JanRSmit/HALS-Mechatronics/BASE/Adjust-Level-M8-Screw.png

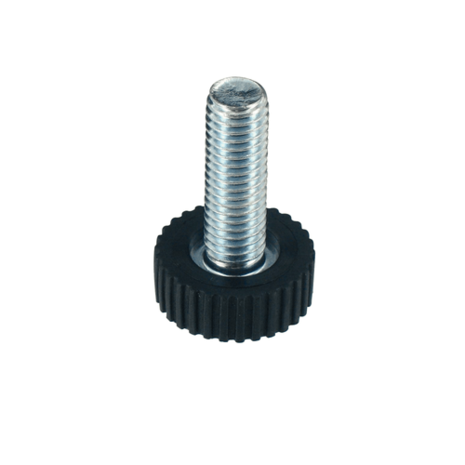
BASE/Adjust-Level-M8-Screw.png
