JanRSmit/HALS-Mechatronics/BASE/Endcap-LevelAdjust-WeightBrackets-02.jpg

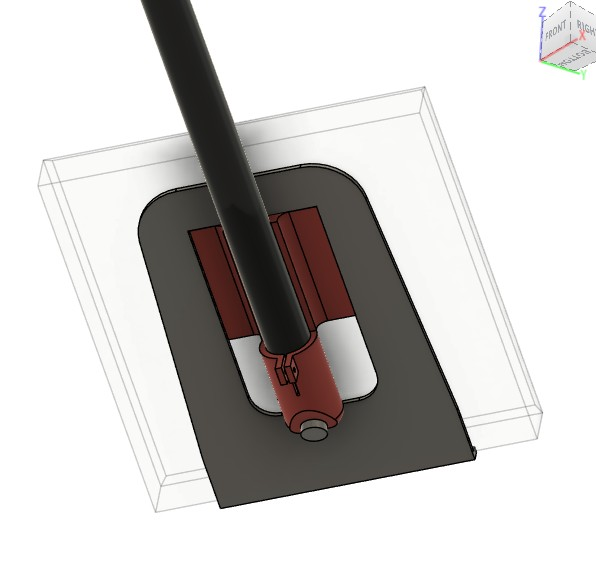
BASE/Endcap-LevelAdjust-WeightBrackets-02.jpg
