JanRSmit/HALS-Mechatronics/BASE/GTSP5212LB_3.jpg

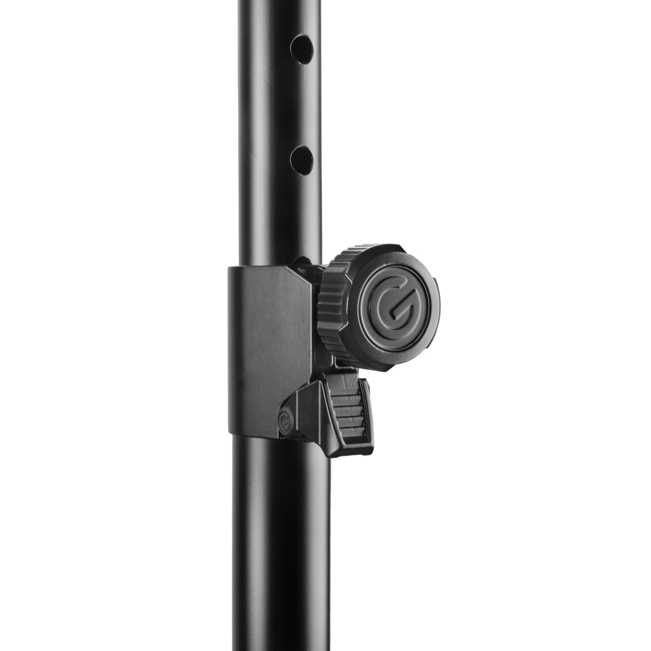
BASE/GTSP5212LB_3.jpg
