JanRSmit/HALS-Mechatronics/Hub-Arm-Assy/Arm-Assy-HUB.png

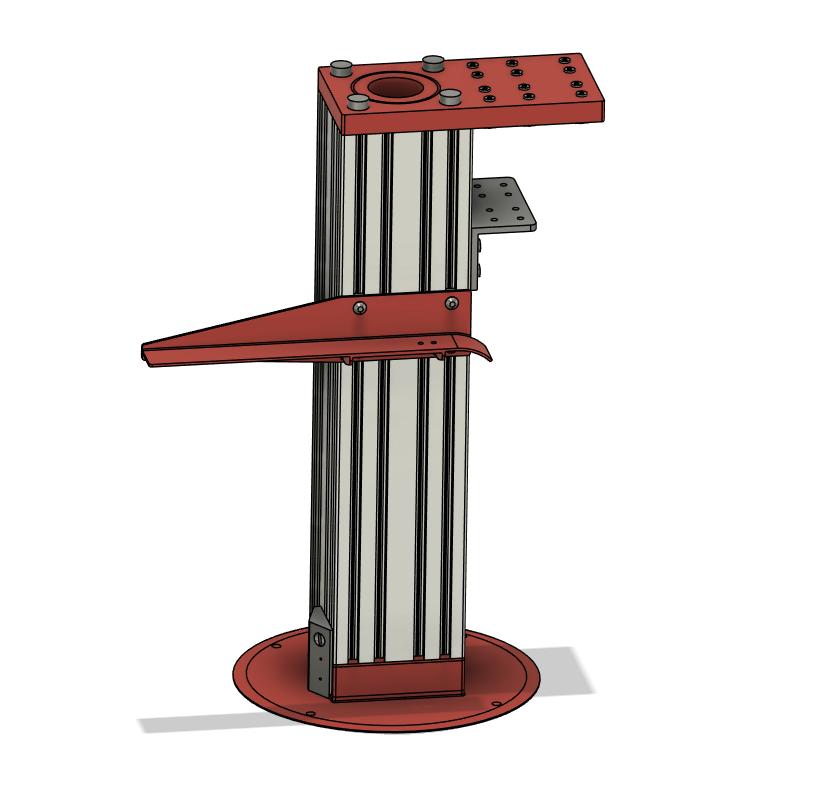
Hub-Arm-Assy/Arm-Assy-HUB.png
