JanRSmit/HALS-Mechatronics/Hub-Arm-Assy/ARM-EIND-SPANBLOK.png

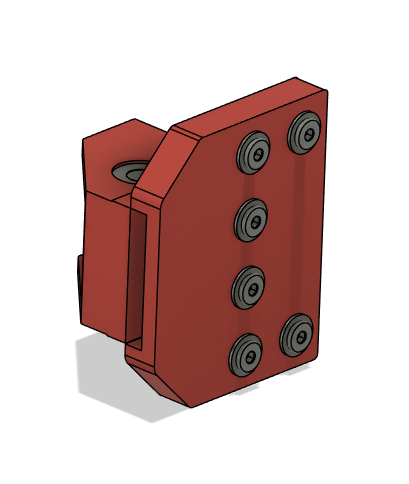
Hub-Arm-Assy/ARM-EIND-SPANBLOK.png
