JanRSmit/HALS-Mechatronics/Hub-Arm-Assy/ARM-MID-Spanblok.png

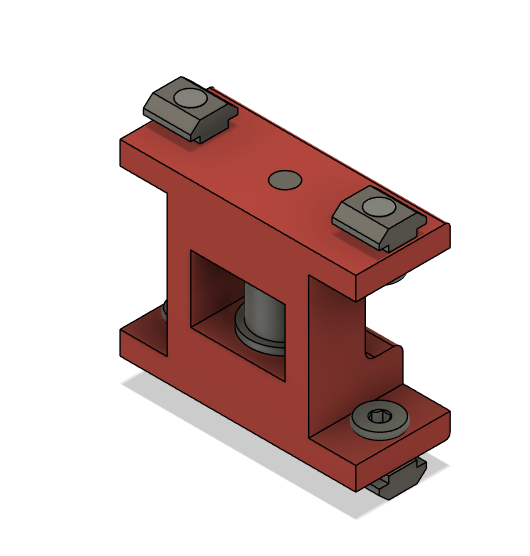
Hub-Arm-Assy/ARM-MID-Spanblok.png
