JanRSmit/HALS-Mechatronics/Hub-Arm-Assy/ARM-MOTOR-MOUNT.png

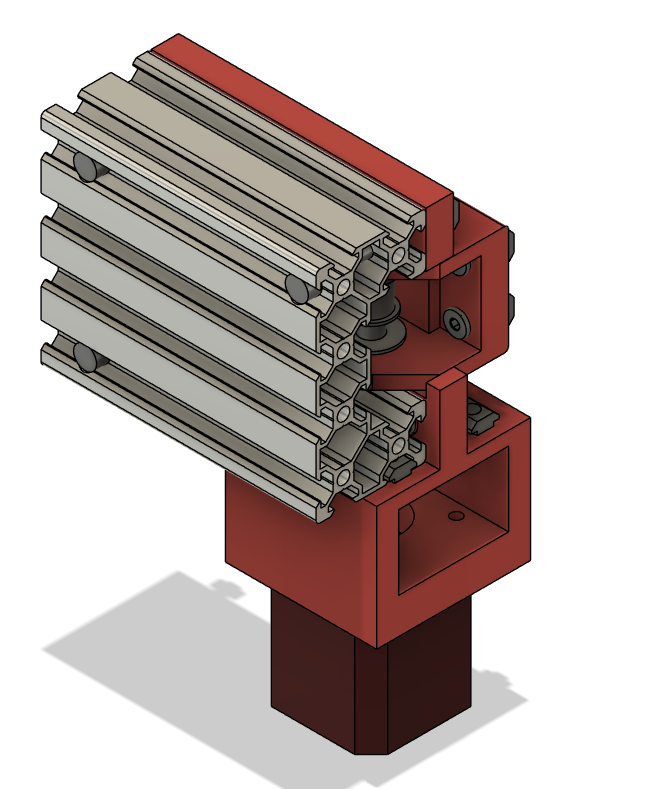
Hub-Arm-Assy/ARM-MOTOR-MOUNT.png
