JanRSmit/HALS-Mechatronics/Hub-Arm-Assy/ECR-P8-6-TPM.jpg

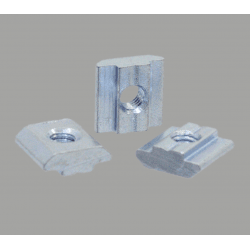
Hub-Arm-Assy/ECR-P8-6-TPM.jpg
