JanRSmit/HALS-Mechatronics/Hub-Arm-Assy/HALS-ROBOT-01.png

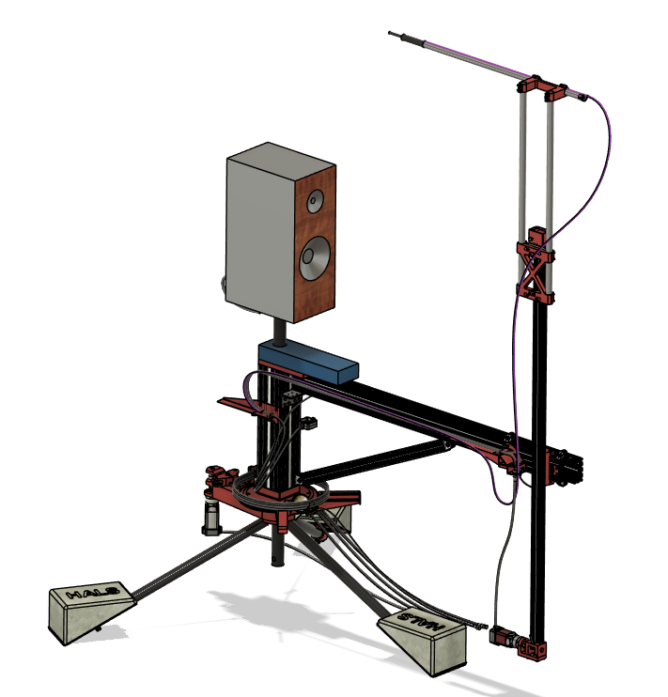
Hub-Arm-Assy/HALS-ROBOT-01.png
