JanRSmit/HALS-Mechatronics/Hub-Arm-Assy/KABEL-HARNAS-Gantry.png

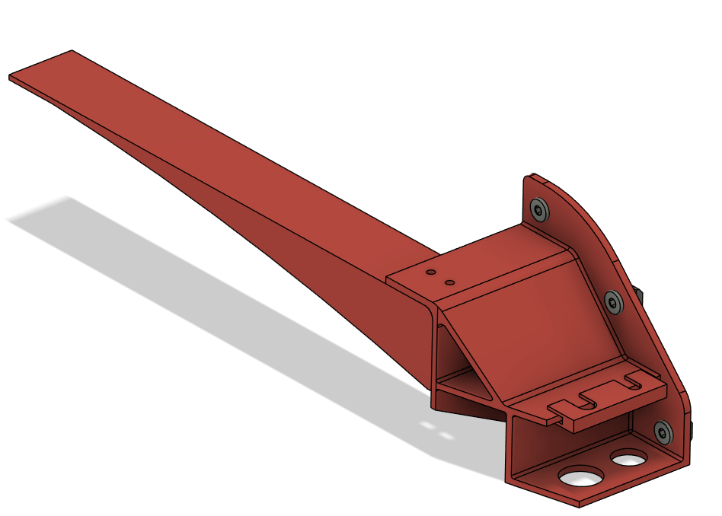
Hub-Arm-Assy/KABEL-HARNAS-Gantry.png
