JanRSmit/HALS-Mechatronics/Hub-Arm-Assy/low-profile-screws-m5x20.jpg

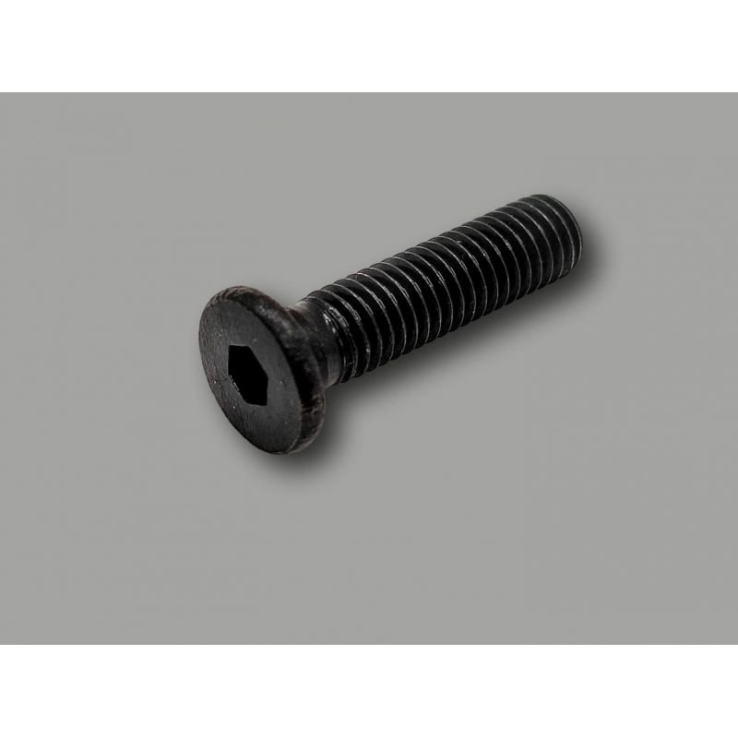
Hub-Arm-Assy/low-profile-screws-m5x20.jpg
