JanRSmit/HALS-Mechatronics/Hub-Arm-Assy/Pivot-joint-for-20x40-profile.jpg

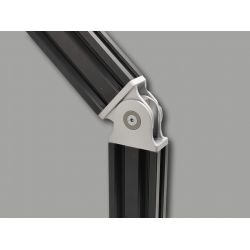
Hub-Arm-Assy/Pivot-joint-for-20x40-profile.jpg
