JanRSmit/HALS-Mechatronics/Hub-Arm-Assy/Top-support-of-Hub-Arm-Assy-vertical-crossection.jpg

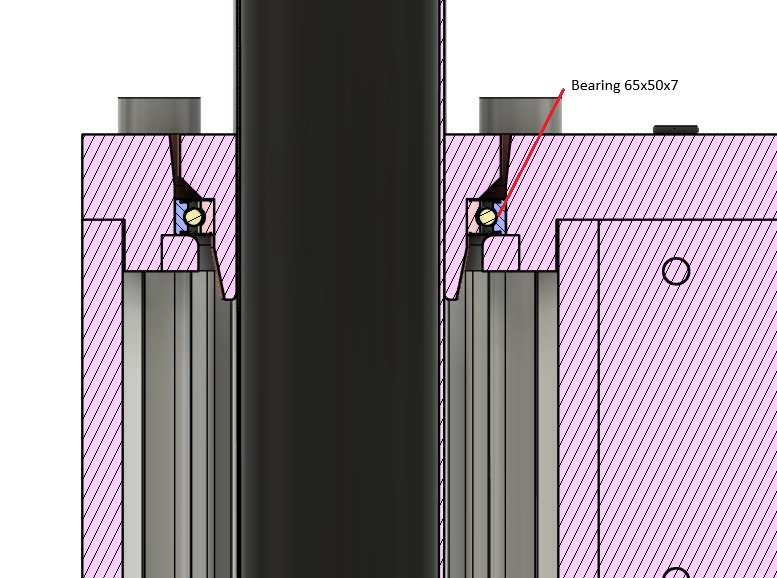
Hub-Arm-Assy/Top-support-of-Hub-Arm-Assy-vertical-crossection.jpg
