JanRSmit/HALS-Mechatronics/MOTION&CABLING/3D-Model-CABLING.jpg

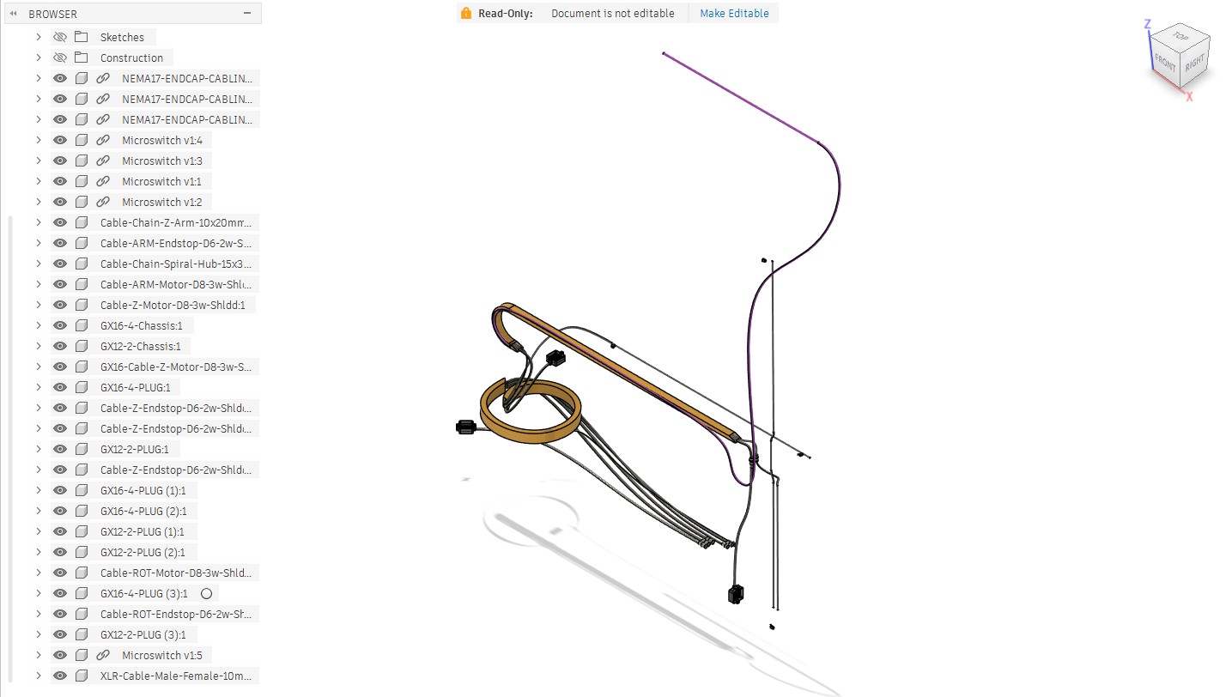
MOTION&CABLING/3D-Model-CABLING.jpg
