JanRSmit/HALS-Mechatronics/MOTION&CABLING/GitHub-MOTION (Electronics-Motors)/BTT-Stuff/GRBLHAL-BTTSKR3EZ-Firmware-01/02-Screenshot 2026-01-21.png

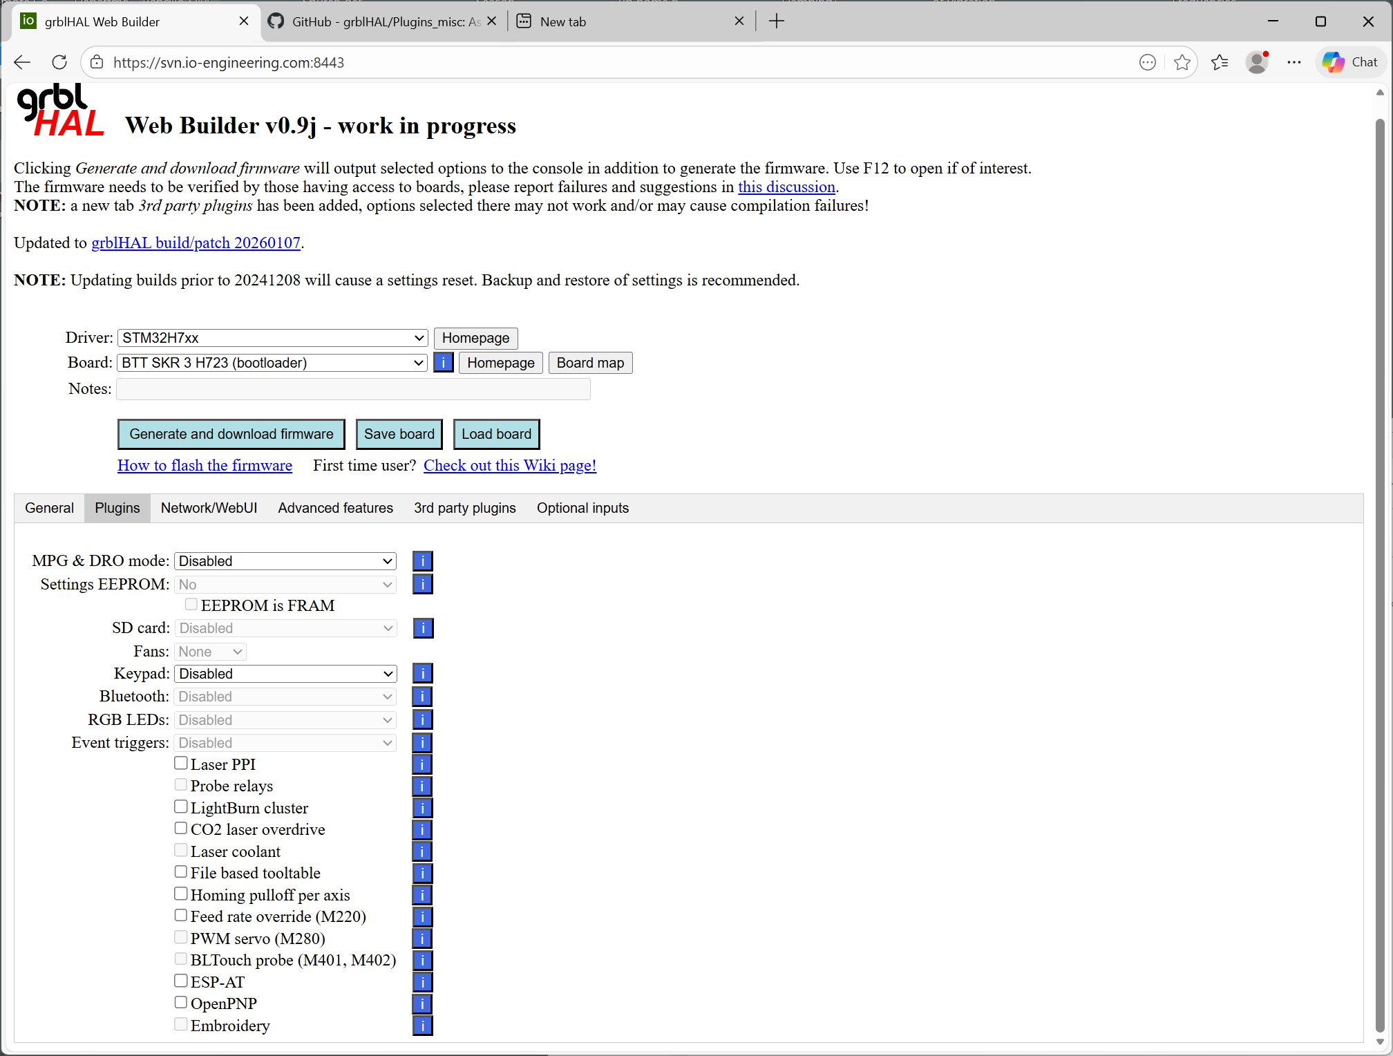
MOTION&CABLING/GitHub-MOTION (Electronics-Motors)/BTT-Stuff/GRBLHAL-BTTSKR3EZ-Firmware-01/02-Screenshot 2026-01-21.png
