JanRSmit/HALS-Mechatronics/MOTION&CABLING/GitHub-MOTION (Electronics-Motors)/BTT-Stuff/Hardware (SKR 3 EZ)/EXT2-Connections-needed.png

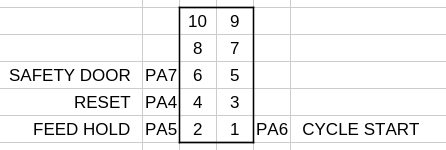
MOTION&CABLING/GitHub-MOTION (Electronics-Motors)/BTT-Stuff/Hardware (SKR 3 EZ)/EXT2-Connections-needed.png
