JanRSmit/HALS-Mechatronics/MOTION&CABLING/Motion-Controller-Schema.jpg

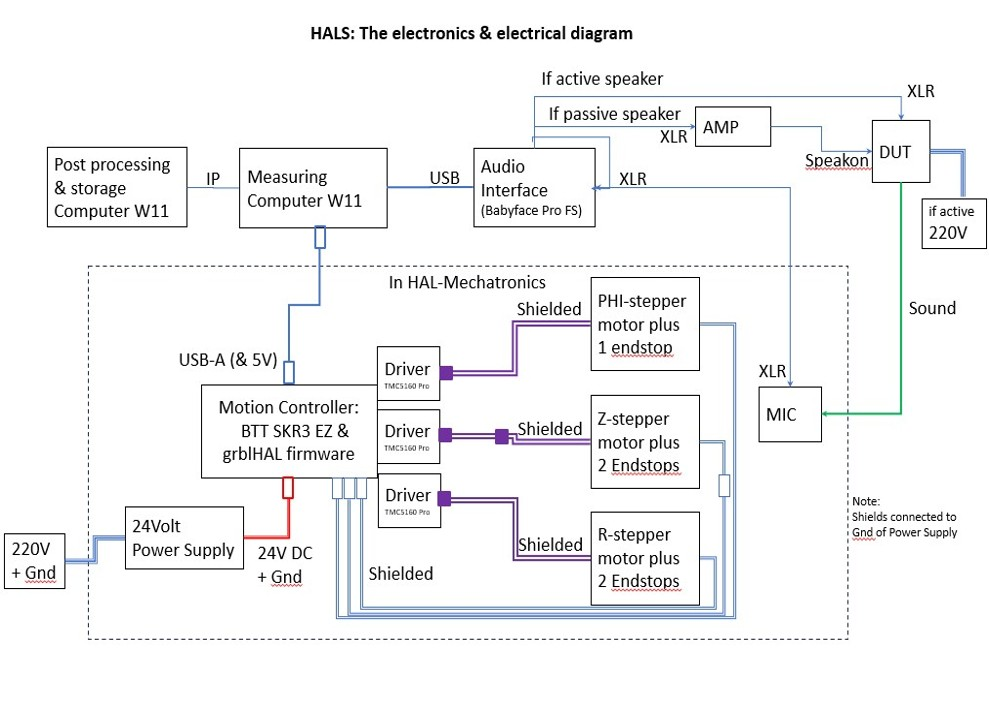
MOTION&CABLING/Motion-Controller-Schema.jpg
