JanRSmit/HALS-Mechatronics/RotatingDrive/Motor-Pulley-Assy-complete.jpg

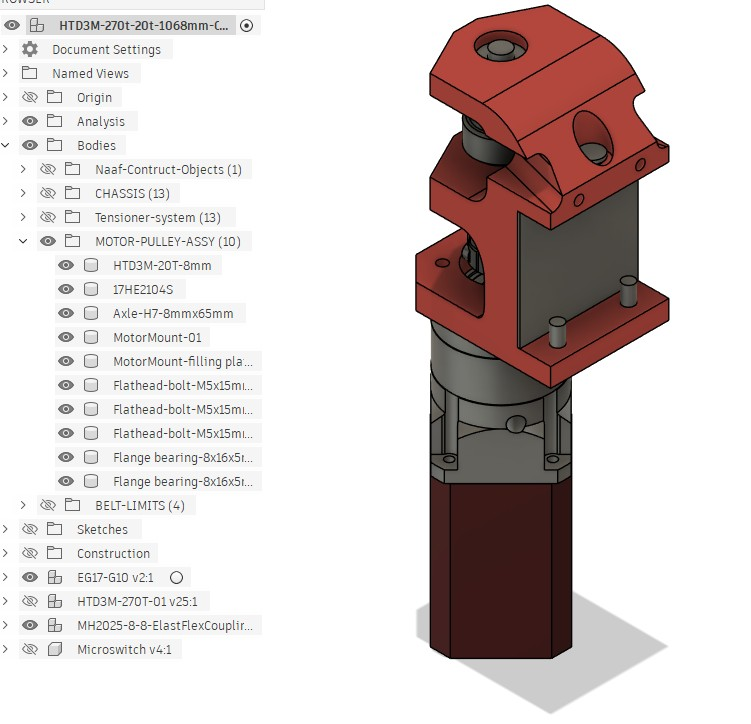
RotatingDrive/Motor-Pulley-Assy-complete.jpg
