JanRSmit/HALS-Mechatronics/RotatingDrive/Nema17-Endcap-Cabling.jpg

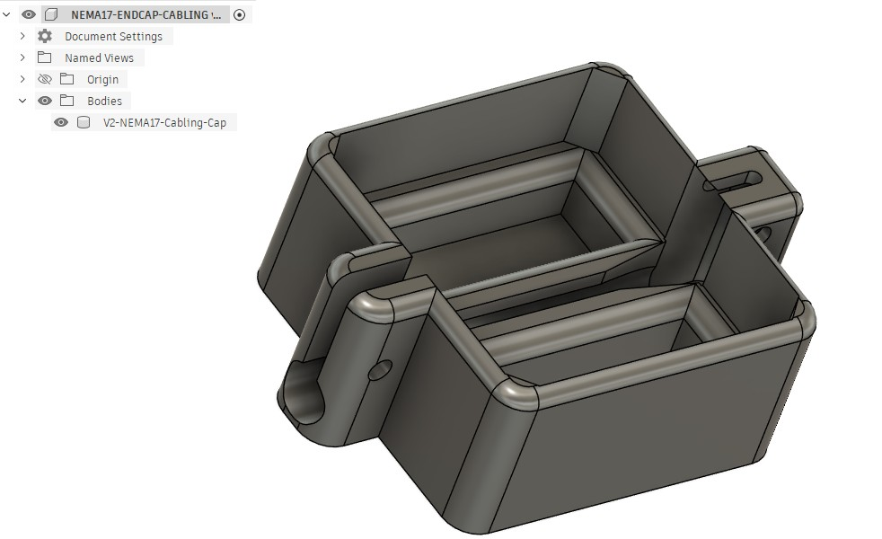
RotatingDrive/Nema17-Endcap-Cabling.jpg
