JanRSmit/HALS-Mechatronics/RotatingDrive/Screenshot 2026-04-07 114829.jpg

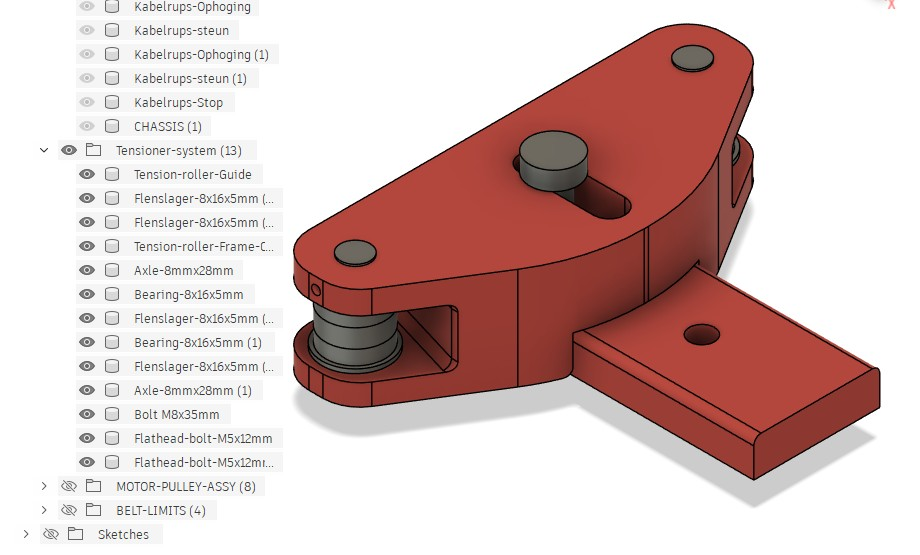
RotatingDrive/Screenshot 2026-04-07 114829.jpg
