JanRSmit/HALS-Mechatronics/RotatingDrive/Tensioner-system-Assy.jpg

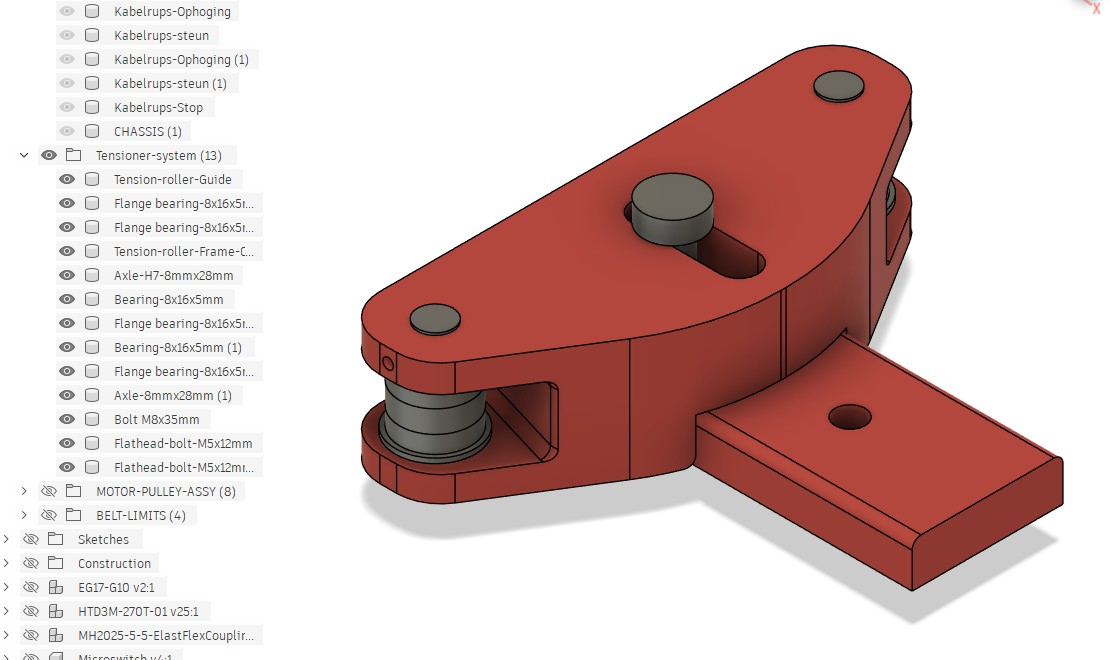
RotatingDrive/Tensioner-system-Assy.jpg
