JanRSmit/HALS-Mechatronics/STOOL/20260924_093839.jpg

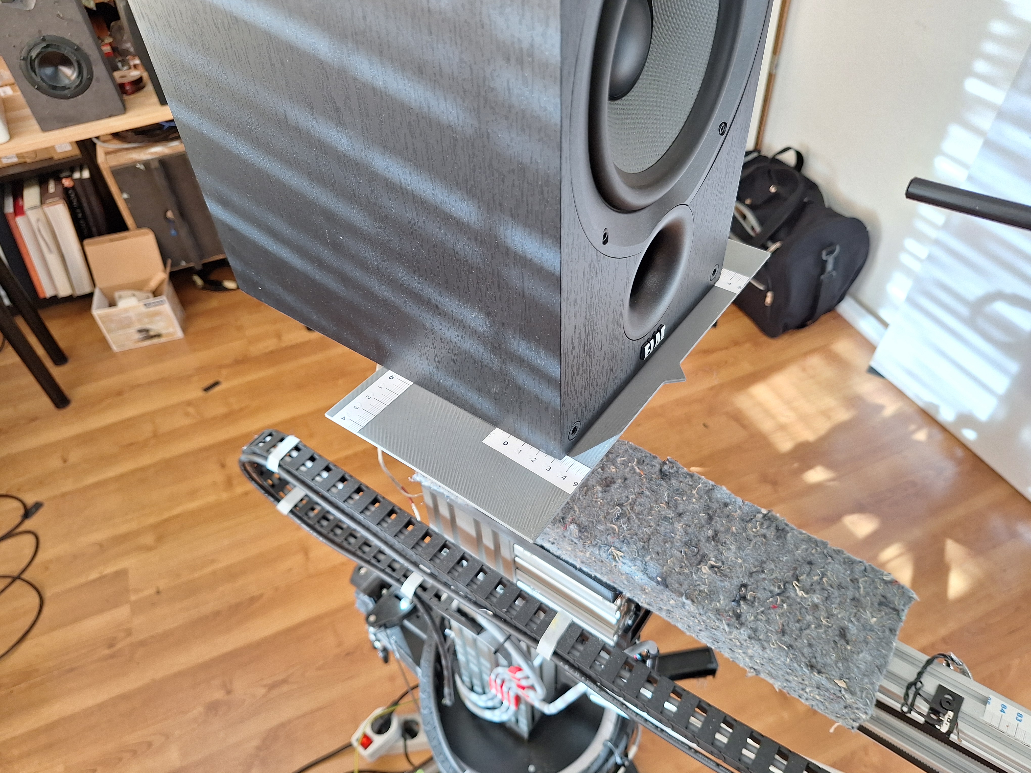
STOOL/20260924_093839.jpg
