JanRSmit/HALS-Mechatronics/STOOL/Stool-9x90mm-incl-CalibTriangle.jpg

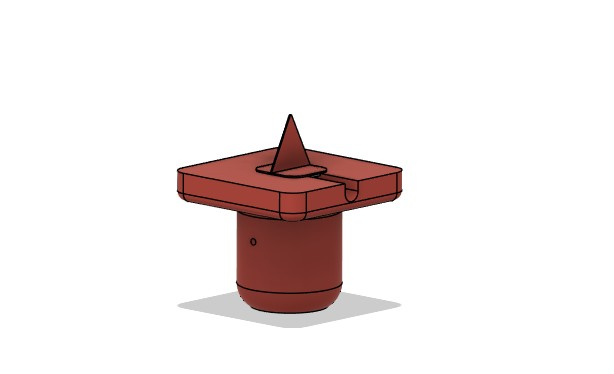
STOOL/Stool-9x90mm-incl-CalibTriangle.jpg
