JanRSmit/HALS-Mechatronics/STOOL/Stool-200x200m-incl-CalibTriangle.jpg

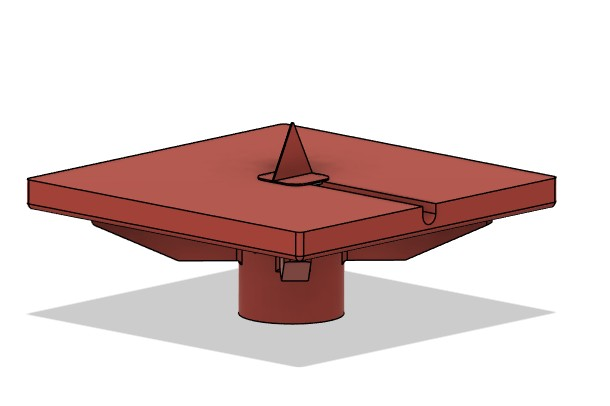
STOOL/Stool-200x200m-incl-CalibTriangle.jpg
