JanRSmit/HALS-Mechatronics/BASE/TripodLeg-Mass-Plateau.step

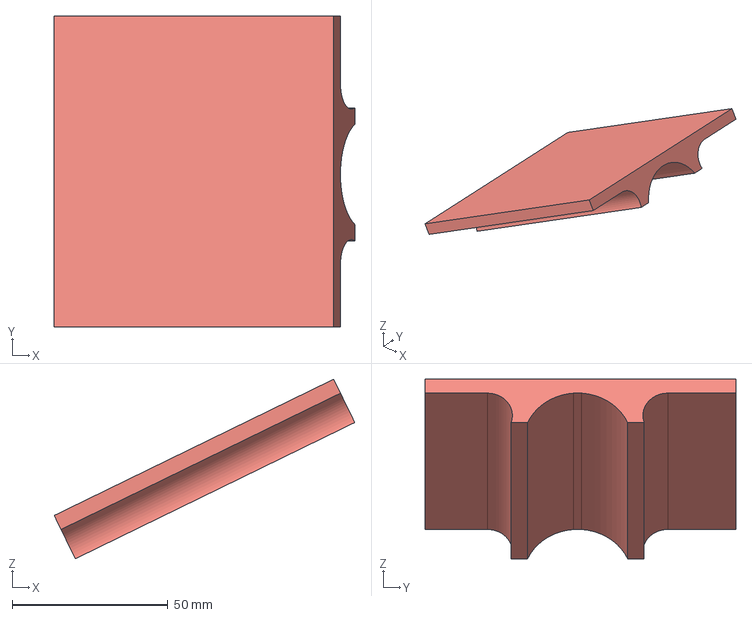
[picture p81: CAD file, 2026-04-06]
BASE/TripodLeg-Mass-Plateau.step
96.7 x 100.0 x 57.8 mm
