JanRSmit/HALS-Mechatronics/RotatingDrive/Tension-Roller-Frame.step

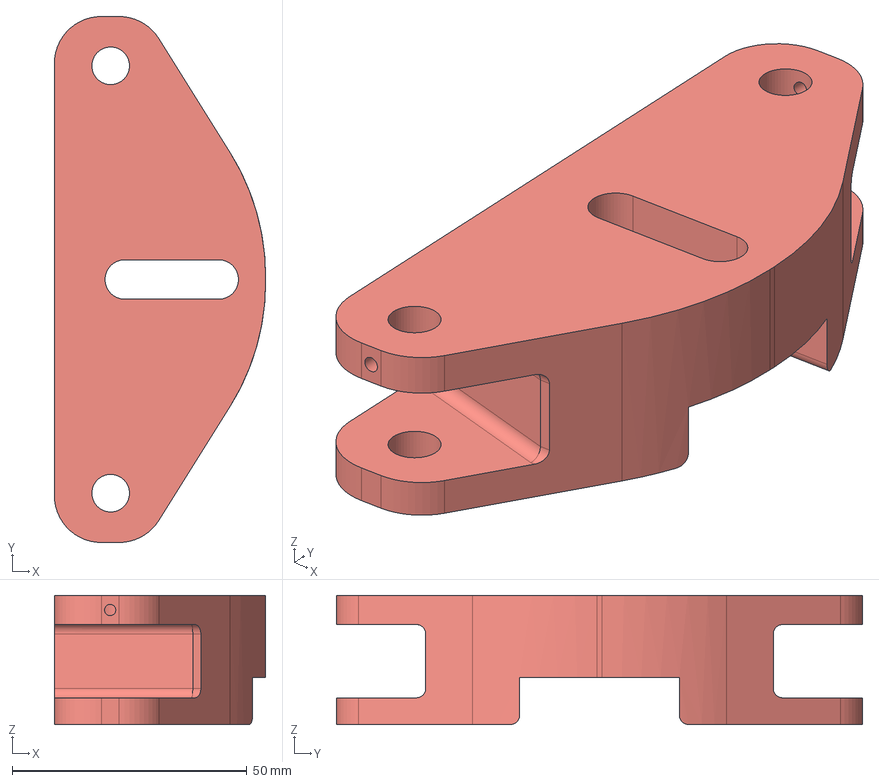
[picture p82: CAD file, 2026-04-07]
RotatingDrive/Tension-Roller-Frame.step
45.0 x 112.0 x 27.5 mm
