JanRSmit/HALS-Mechatronics/BASE/TripodLeg-Endcaps.step

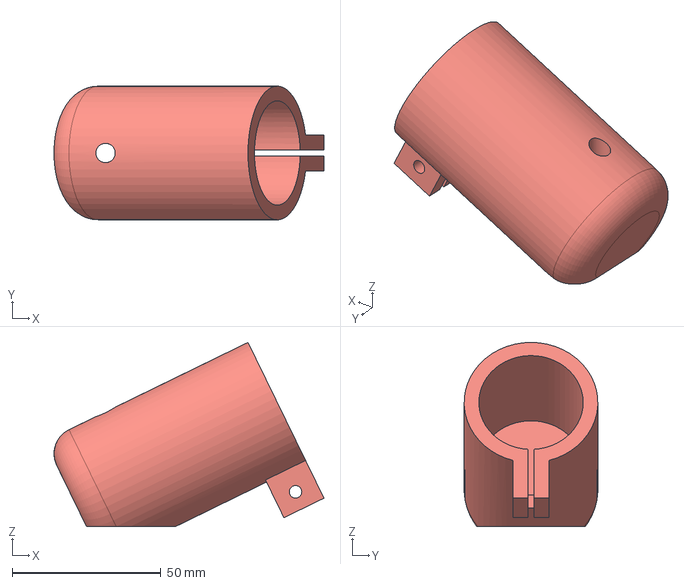
[picture p83: CAD file, 2026-04-06]
BASE/TripodLeg-Endcaps.step
90.8 x 45.0 x 62.0 mm
