JanRSmit/HALS-Mechatronics/RotatingDrive/CableChain-Mount-Chassis-Side.step

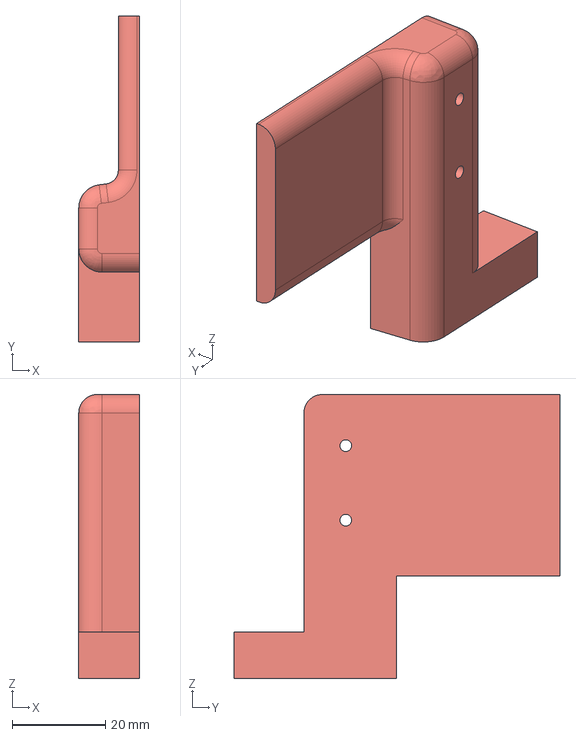
[picture p84: CAD file, 2026-04-07]
RotatingDrive/CableChain-Mount-Chassis-Side.step
13.0 x 70.0 x 61.0 mm
