JanRSmit/HALS-Mechatronics/BASE/TripodLeg-Endcap-WeightBrackes-adjust-foot.step

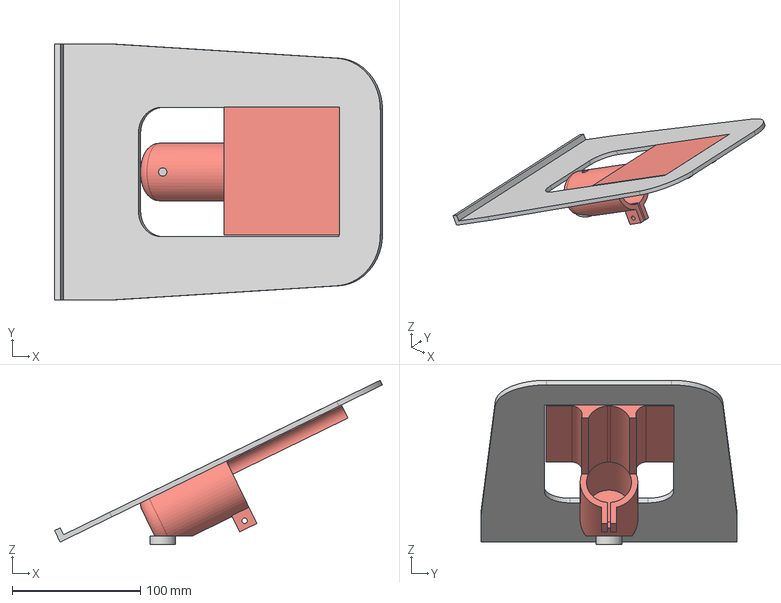
[picture p85: CAD file, 2026-03-27]
BASE/TripodLeg-Endcap-WeightBrackes-adjust-foot.step
256.0 x 200.0 x 128.4 mm
