JanRSmit/HALS-Mechatronics/RotatingDrive/Cablechain-Support-Part-2.step

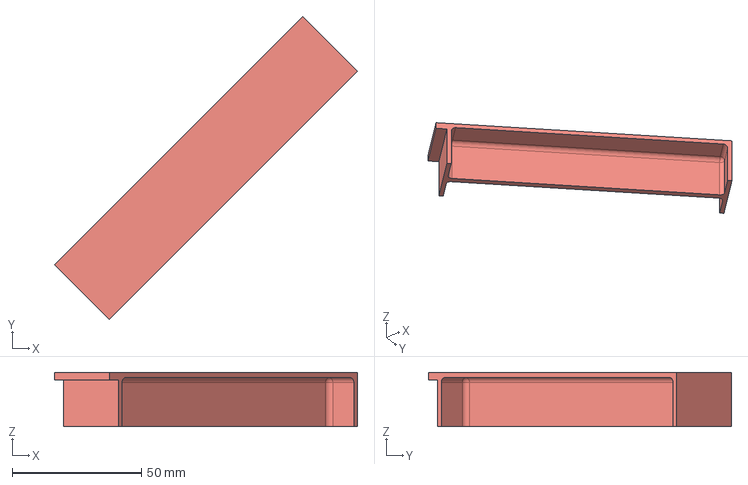
[picture p86: CAD file, 2026-04-07]
RotatingDrive/Cablechain-Support-Part-2.step
117.4 x 117.4 x 21.0 mm
