JanRSmit/HALS-Mechatronics/RotatingDrive/NEMA17-ENDCAP-CABLING.step

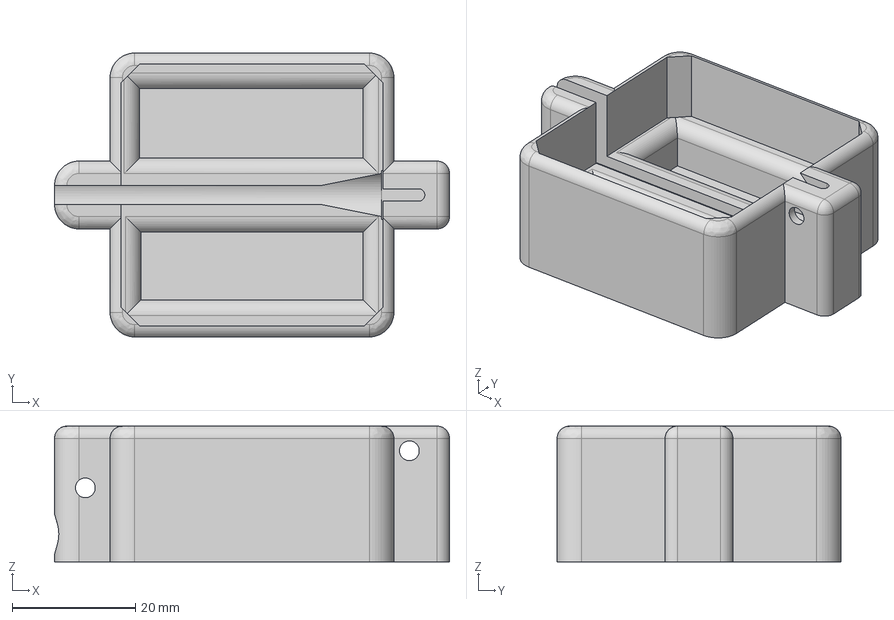
[picture p87: CAD file, 2026-04-07]
RotatingDrive/NEMA17-ENDCAP-CABLING.step
64.0 x 46.0 x 22.0 mm
