JanRSmit/HALS-Mechatronics/RotatingDrive/MSwitch-Bracket-Clamp.step

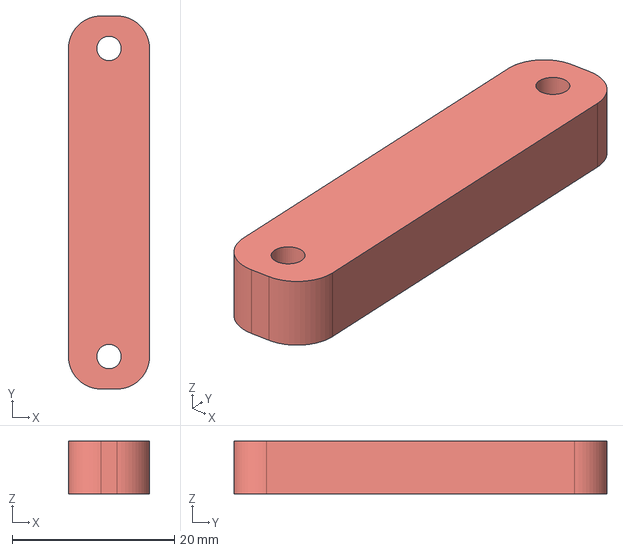
[picture p88: CAD file, 2026-04-07]
RotatingDrive/MSwitch-Bracket-Clamp.step
10.0 x 46.0 x 6.50 mm
