JanRSmit/HALS-Mechatronics/RotatingDrive/Tension-Roller-Guide.step

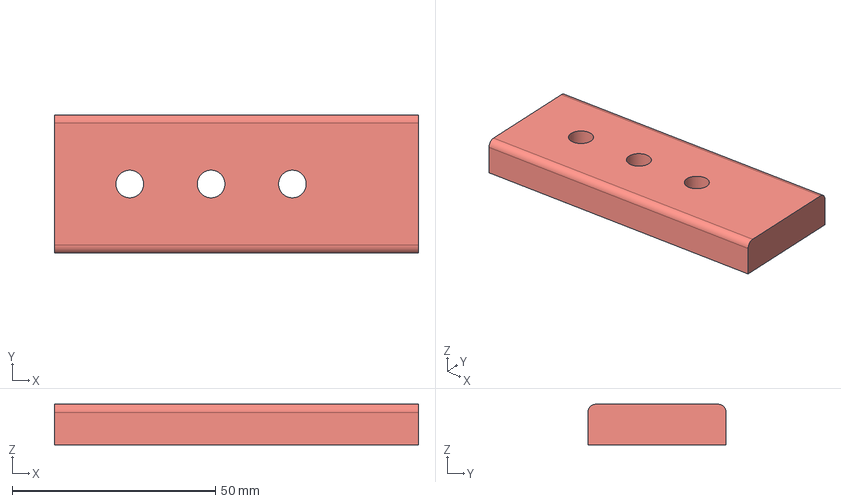
[picture p89: CAD file, 2026-04-07]
RotatingDrive/Tension-Roller-Guide.step
89.5 x 34.0 x 10.0 mm
