JanRSmit/HALS-Mechatronics/RotatingDrive/HTD3M-270t-20t-1068mm-Chassis-CHASSIS.step

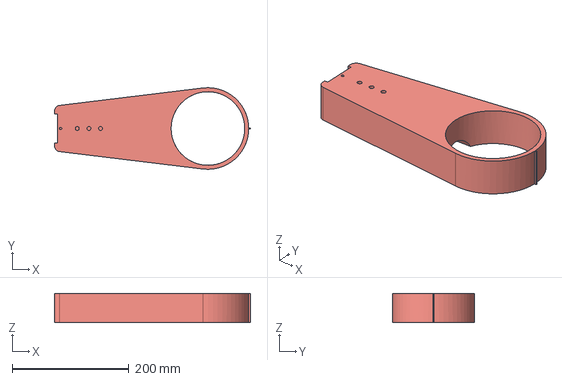
[picture p90: CAD file, 2026-04-06]
RotatingDrive/HTD3M-270t-20t-1068mm-Chassis-CHASSIS.step
336.0 x 140.0 x 50.0 mm
