JanRSmit/HALS-Mechatronics/RotatingDrive/HTD3M-270t-20t-1068mm-Chassis-MotorMount-01.step

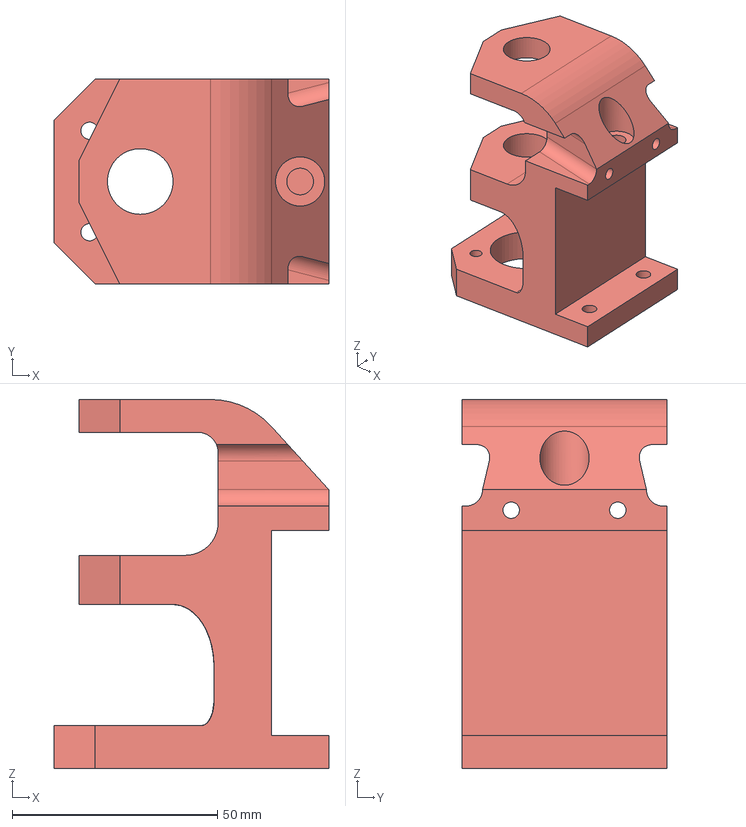
[picture p91: CAD file, 2026-04-06]
RotatingDrive/HTD3M-270t-20t-1068mm-Chassis-MotorMount-01.step
67.0 x 50.0 x 90.0 mm
