JanRSmit/HALS-Mechatronics/RotatingDrive/HTD3M-270t-20t-1068mm-Chassis-HUB.step

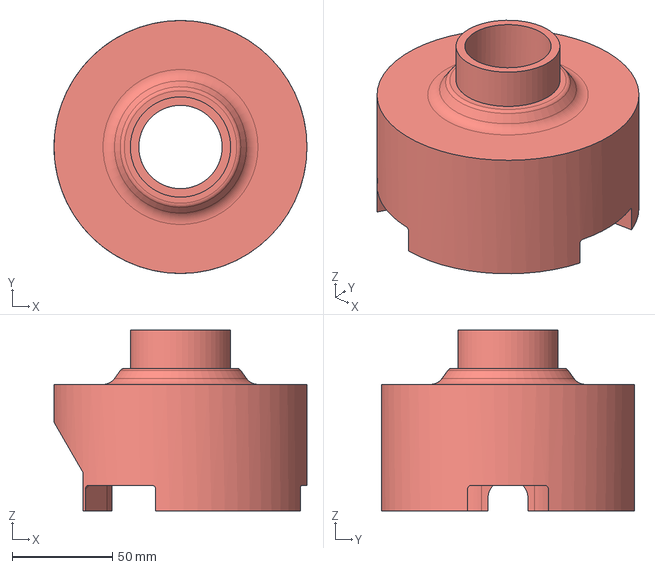
[picture p92: CAD file, 2026-04-06]
RotatingDrive/HTD3M-270t-20t-1068mm-Chassis-HUB.step
126.0 x 126.0 x 90.0 mm
