JanRSmit/HALS-Mechatronics/MOTION&CABLING/Connect-cable-to-Endstop-1.jpg

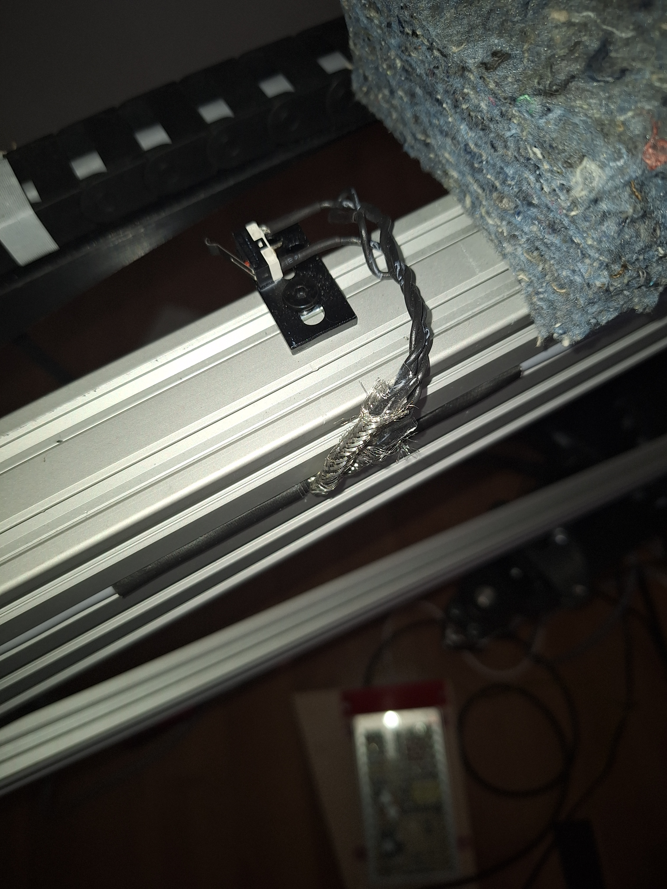
MOTION&CABLING/Connect-cable-to-Endstop-1.jpg
