JanRSmit/HALS-Mechatronics/MOTION&CABLING/Connect-cable-to-Endstop-2.jpg

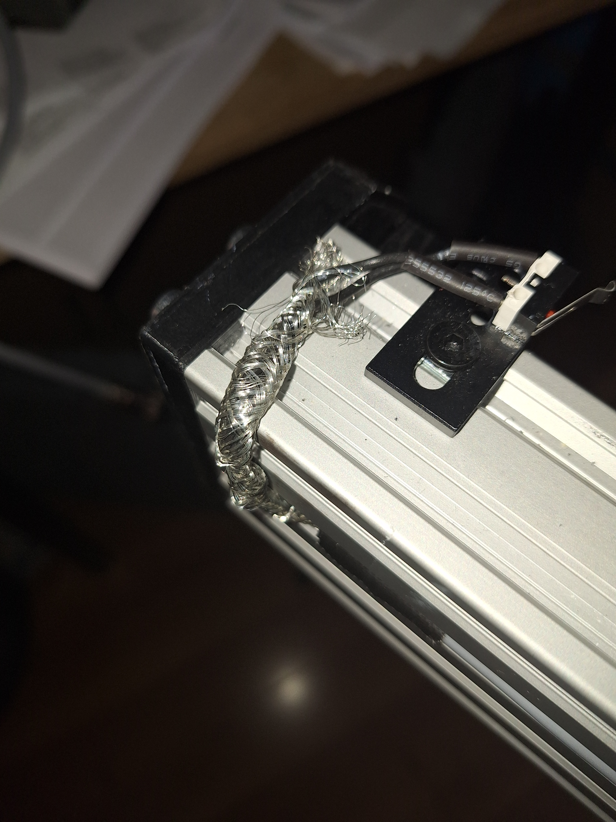
MOTION&CABLING/Connect-cable-to-Endstop-2.jpg
