JanRSmit/HALS-Mechatronics/MOTION&CABLING/Connect-cable-to-Endstop-3.jpg

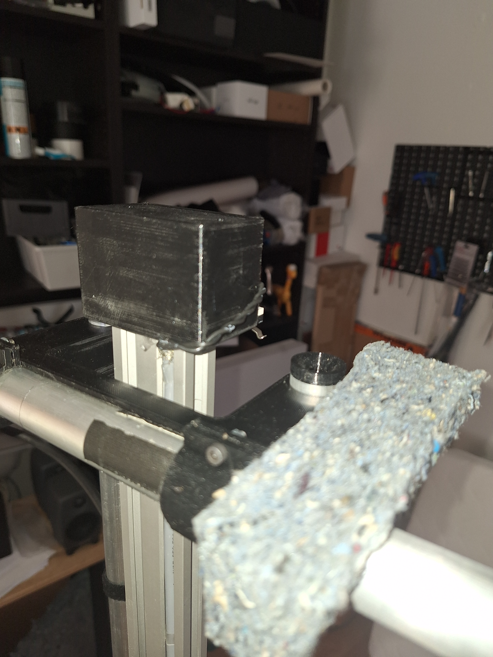
MOTION&CABLING/Connect-cable-to-Endstop-3.jpg
