JanRSmit/HALS-Mechatronics/MOTION&CABLING/Endcap-on-Motor.jpg

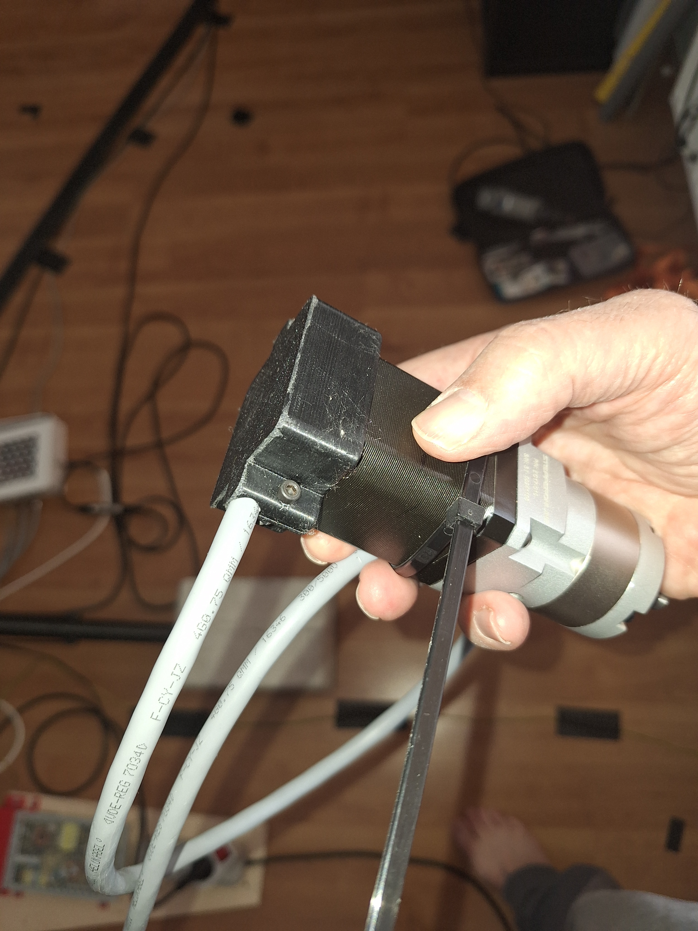
MOTION&CABLING/Endcap-on-Motor.jpg
