JanRSmit/HALS-Mechatronics/STOOL/20260924_093724.jpg

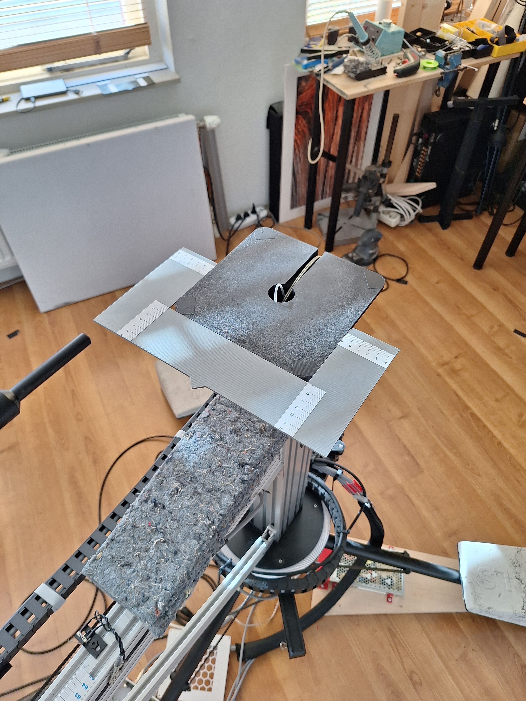
STOOL/20260924_093724.jpg
