JanRSmit/HALS-Mechatronics/STOOL/20261001_090428.jpg

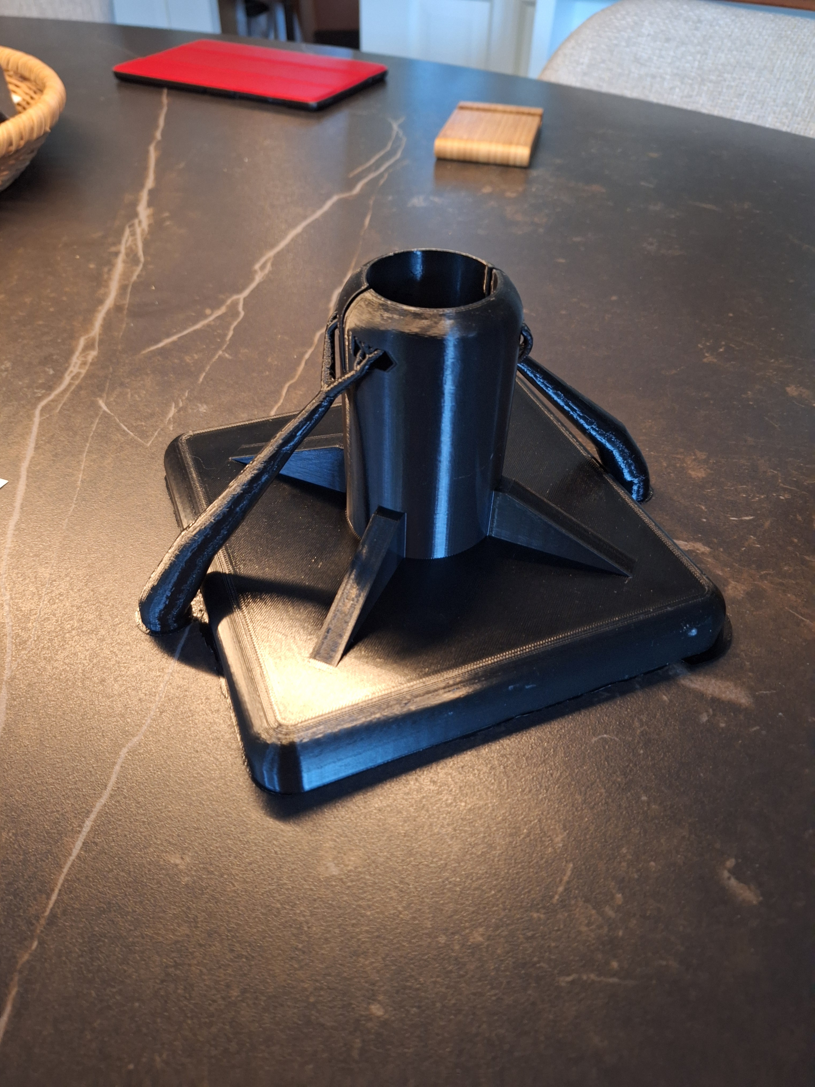
STOOL/20261001_090428.jpg
