JanRSmit/HALS-Mechatronics/STOOL/20261001_090448.jpg

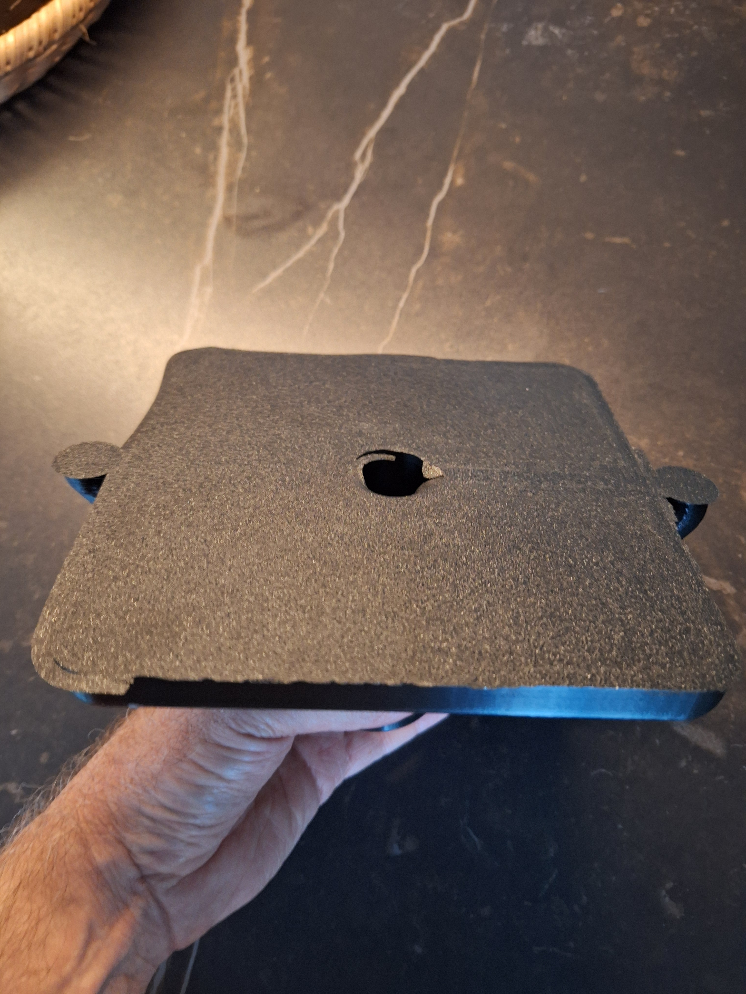
STOOL/20261001_090448.jpg
