JanRSmit/HALS-Mechatronics/STOOL/20261001_092008.jpg

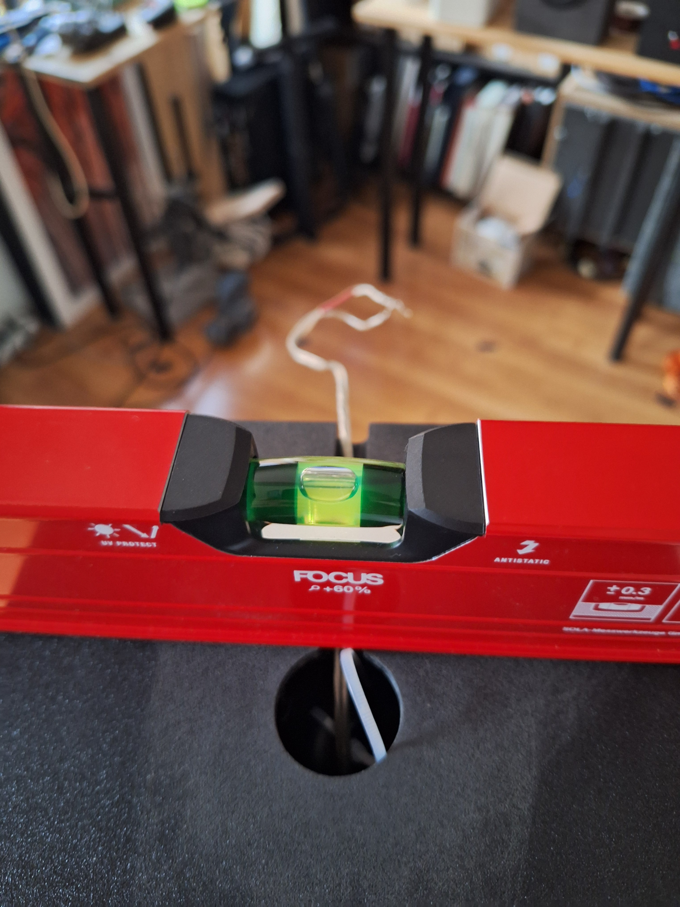
STOOL/20261001_092008.jpg
