JanRSmit/HALS-Mechatronics/MOTION&CABLING/Wiring in the controller case.jpg

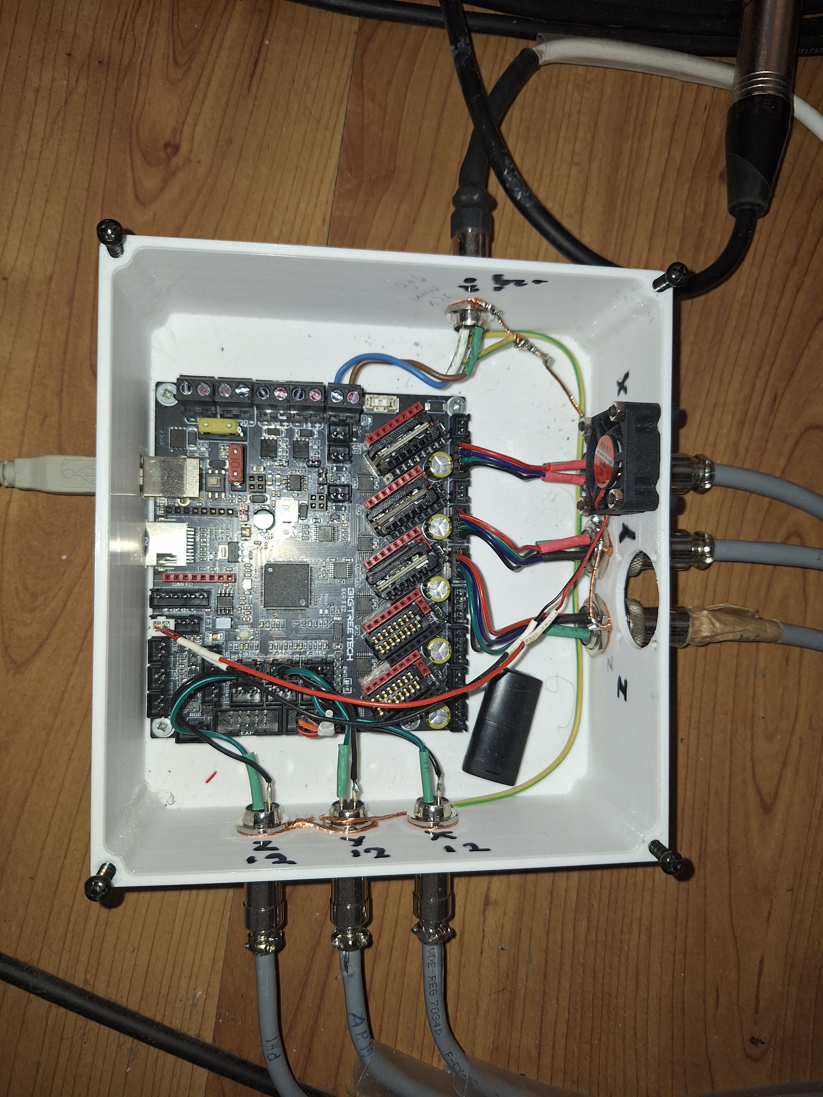
MOTION&CABLING/Wiring in the controller case.jpg
